PeraZver/Microwave-Transmitter/SW/Firmware/RSSI_Readout/RSSI_Readout.ino

/* 
 *  ADC readout from RSSI detectors LMH2120.
 *  
 *  Example based on example for analogRead from Teensy examples.
*  You can change the number of averages, bits of resolution and also the comparison value or range.
*  
*  Pero, August 2017
*/


#include <ADC.h>

const int readPin = A0; // ADC0
const int readPin2 = A1; // ADC1

ADC *adc = new ADC(); // adc object;

void setup() {

    pinMode(readPin, INPUT); 
    pinMode(readPin2, INPUT); 


    Serial.begin(9600);

    Serial.println("RSSI detectors interface");
    Serial.println("v0.0");
    Serial.println("Pero, August 2017");
    Serial.println("");

    ///// ADC0 ////
    // reference can be ADC_REF_3V3, ADC_REF_1V2 (not for Teensy LC) or ADC_REF_EXT.
    //adc->setReference(ADC_REF_1V2, ADC_0); // change all 3.3 to 1.2 if you change the reference to 1V2

    adc->setAveraging(32); // set number of averages
    adc->setResolution(12); // set bits of resolution

    // it can be ADC_VERY_LOW_SPEED, ADC_LOW_SPEED, ADC_MED_SPEED, ADC_HIGH_SPEED_16BITS, ADC_HIGH_SPEED or ADC_VERY_HIGH_SPEED
    // see the documentation for more information
    adc->setConversionSpeed(ADC_HIGH_SPEED); // change the conversion speed
    // it can be ADC_VERY_LOW_SPEED, ADC_LOW_SPEED, ADC_MED_SPEED, ADC_HIGH_SPEED or ADC_VERY_HIGH_SPEED
    adc->setSamplingSpeed(ADC_HIGH_SPEED); // change the sampling speed

    //adc->enableInterrupts(ADC_0);

    // always call the compare functions after changing the resolution!
    //adc->enableCompare(1.0/3.3*adc->getMaxValue(ADC_0), 0, ADC_0); // measurement will be ready if value < 1.0V
    //adc->enableCompareRange(1.0*adc->getMaxValue(ADC_0)/3.3, 2.0*adc->getMaxValue(ADC_0)/3.3, 0, 1, ADC_0); // ready if value lies out of [1.0,2.0] V

    ////// ADC1 /////
    #if ADC_NUM_ADCS>1
    adc->setAveraging(32, ADC_1); // set number of averages
    adc->setResolution(16, ADC_1); // set bits of resolution
    adc->setConversionSpeed(ADC_VERY_LOW_SPEED, ADC_1); // change the conversion speed
    adc->setSamplingSpeed(ADC_VERY_LOW_SPEED, ADC_1); // change the sampling speed

    // always call the compare functions after changing the resolution!
    //adc->enableCompare(1.0/3.3*adc->getMaxValue(ADC_1), 0, ADC_1); // measurement will be ready if value < 1.0V
    //adc->enableCompareRange(1.0*adc->getMaxValue(ADC_1)/3.3, 2.0*adc->getMaxValue(ADC_1)/3.3, 0, 1, ADC_1); // ready if value lies out of [1.0,2.0] V
    #endif

    Serial.println("End setup");

}

int value;
int value2;

void loop() {

    value = adc->analogRead(readPin); // read a new value, will return ADC_ERROR_VALUE if the comparison is false.

    Serial.print("Pin: ");
    Serial.print(readPin);
    Serial.print(", value ADC0: ");
    Serial.println(value*3.3/adc->getMaxValue(ADC_0), DEC);

    #if ADC_NUM_ADCS>1
    value2 = adc->analogRead(readPin2, ADC_1);

    Serial.print("Pin: ");
    Serial.print(readPin2);
    Serial.print(", value ADC1: ");
    Serial.println(value2*3.3/adc->getMaxValue(ADC_1), DEC);
    #endif

    /* fail_flag contains all possible errors,
        They are defined in  ADC_Module.h as

        ADC_ERROR_OTHER
        ADC_ERROR_CALIB
        ADC_ERROR_WRONG_PIN
        ADC_ERROR_ANALOG_READ
        ADC_ERROR_COMPARISON
        ADC_ERROR_ANALOG_DIFF_READ
        ADC_ERROR_CONT
        ADC_ERROR_CONT_DIFF
        ADC_ERROR_WRONG_ADC
        ADC_ERROR_SYNCH

        You can compare the value of the flag with those masks to know what's the error.
    */

    if(adc->adc0->fail_flag) {
        Serial.print("ADC0 error flags: 0x");
        Serial.println(adc->adc0->fail_flag, HEX);
        if(adc->adc0->fail_flag == ADC_ERROR_COMPARISON) {
            adc->adc0->fail_flag &= ~ADC_ERROR_COMPARISON; // clear that error
            Serial.println("Comparison error in ADC0");
        }
    }
    #if ADC_NUM_ADCS>1
    if(adc->adc1->fail_flag) {
        Serial.print("ADC1 error flags: 0x");
        Serial.println(adc->adc1->fail_flag, HEX);
        if(adc->adc1->fail_flag == ADC_ERROR_COMPARISON) {
            adc->adc1->fail_flag &= ~ADC_ERROR_COMPARISON; // clear that error
            Serial.println("Comparison error in ADC1");
        }
    }
    #endif

    digitalWriteFast(LED_BUILTIN, !digitalReadFast(LED_BUILTIN));

    delay(500);
}

// If you enable interrupts make sure to call readSingle() to clear the interrupt.
void adc0_isr() {
        adc->adc0->readSingle();
}
