PeraZver/Microwave-Transmitter/SW/Firmware/Basic/src/MAX2871.cpp

#include <MAX2871.h>

//Setting temperature read and MUX readout
uint32_t regInitValues[6] = { EN_INT | N_SET | F_SET | REG_0,
                              CPL | CPT | PHASE | M_SET | REG_1,
                              0x00005E42 | LDF,
                              0xE8000013,
                              0x618160DC | DIVA,
                              0x00400005 | F01}; // MUX[3] = 1, ADCM = 001, ADCS = 1

uint32_t MAX2871_Registers[6] = {0}; //Working registers, that will be changed in code
// ADC selection varible
byte adc_mode = 0b001;  // 001 for temperature, 100 for V tune.

SPISettings MAX2871_SPISettings(1000000, MSBFIRST, SPI_MODE0);



void MAX2871_Init (){
  //Upon power-up, the registers should be programmed
  //twice with at least a 20ms pause between writes.
  //Register programming order should be address 0x05,
  //0x04, 0x03, 0x02, 0x01, and 0x00.

  // Enable MAX3871 chip
  pinMode(MAX2871_CE, OUTPUT);
  digitalWrite(MAX2871_CE, HIGH);

  // set the slave select pin as an output:
  pinMode (MAX2871_SS, OUTPUT);
  digitalWrite (MAX2871_SS, HIGH);

  //Disable RF output
  pinMode(MAX2871_RF_EN, OUTPUT);
  digitalWrite (MAX2871_RF_EN, LOW);

  // Writing 2 times
  for (int j = 0; j < 2; j++){
    for (int i = 5; i >= 0; i--){   // 6 write registers
        MAX2871_SPI_tx (regInitValues[i]);
        MAX2871_Registers[i] = regInitValues[i];    // write init values into working registers
    }
    delay(20);
  }

   MAX2871_SPI_Init();
}

void MAX2871_Read(char adc_select){
  /*
   * Reading register 6 over SPI. Register contains data from ADC and VCO selection.
   * ADC can read either temperature or VCO tuning voltage.
   */

   uint32_t spi_data = 0;
   uint8_t spi_packet[4] = {0};
   uint8_t ADC_data = 0;
   float data = 0;
   signed char i;

   Serial.println("Setting MAX2871 ADC ...");

   switch (adc_select){   // Choose whether to read temperature or VCO voltage
     case 'v':
         adc_mode = 0b100;
         break;

     case 't':
         adc_mode = 0b001;
         break;

    default:   // default value is read temperature
        adc_mode = 0b001;
   }

   MAX2871_ADC_Init();

   Serial.println("Reading data from MAX2871 ...");
   MAX2871_SPI_tx(spi_data | 6);   // "... last 3 bits must be 110 to indicate register 6."

   SPI.beginTransaction(MAX2871_SPISettings);  // start new clock sequence. No need to change SS to low.
   for ( i = 0; i < 4; i++)   {
       spi_packet[i] = SPI.transfer(0x00);   // read from SPI shift register 4 times
   }
   SPI.endTransaction();

   Serial.println("Data read:");
   for ( i = 0; i < 4; i++){
     //Serial.println(spi_packet[i], HEX);
     spi_data |= spi_packet[i];
     if ( i != 3)
         spi_data = spi_data << 8;
   }
   spi_data = spi_data << 2; //one clk period delay
   Serial.println(spi_data, HEX);
   Serial.println("Reading done!");

   if (spi_data & ADCV)
     Serial.println("ADC data valid!");
   else
     Serial.println("ADC data invalid!");
   ADC_data = ( spi_data & ADC_mask ) >> 16;
   Serial.print("ADC data: ");
   Serial.print(ADC_data);

  if (adc_mode == 1){
      data = 95 - 1.14*ADC_data;
      Serial.print("\nTemperature: ");
  }
  else{
      data = 0.315 + 0.0165*ADC_data;
      Serial.print("\nVCO voltage: ");
  }
  Serial.print(data);


  if (spi_data & VASA)
    Serial.println("\nVCO Autoselect searching");
  else
    Serial.println("\nVAS Completed");

  Serial.print("Current VCO: ");
  Serial.println((spi_data & V) >> 3);
  //Serial.println("Reseting ADC");
  MAX2871_ADC_Reset();
}

void MAX2871_SPI_tx(uint32_t spi_data){
  /*
   * This function takes 32-bit data and parses it on four 8-bit packets that Teensy transmitts. The 29 most-significant
   * bits (MSBs) are data, and the three least-significant bits (LSBs) are the register address.
   */

    signed char i = 0;
    uint8_t spi_package[4] = {0};
    // store 32-bit integer into 4 bytes
    for ( i = 0; i < 4; i++) {
       spi_package[i] = (spi_data & (0xFF << 8*i)) >> ( 8*i ) ;
       //Serial.println(spi_package[i], HEX);
    }

    //Serial.println("Sending data to MAX2871: ");
    //Serial.println(spi_data, HEX);
    digitalWrite(MAX2871_SS,LOW);
    SPI.beginTransaction(MAX2871_SPISettings);

    for ( i = 3; i >= 0; i--)
         SPI.transfer(spi_package[i]);

    digitalWrite(MAX2871_SS,HIGH);
    SPI.endTransaction();
    //Serial.println("SPI done!");
    delay(20);
}

void MAX2871_ADC_Init(void){
  /*
   * Initialize ADC in MAX2871 for temperature or tune voltage readout. Must be
   * sequentially written, otherwise it won't work.
   */
   byte ADCM;
   ADCM = adc_mode << 3;

   MAX2871_Registers[3] |= CDIV;
   MAX2871_SPI_tx(MAX2871_Registers[3]);
   MAX2871_Registers[5] |= ADCM;
   MAX2871_SPI_tx(MAX2871_Registers[5]);
   MAX2871_Registers[5] |= ADCS;
   MAX2871_SPI_tx(MAX2871_Registers[5]);
   delay(0.1);
}

void MAX2871_ADC_Reset(void){
 /*
 * Apparently ADC won't work if ADCS is constantly on. For that reason, I'll need to reset it after every read.
 */
 MAX2871_Registers[5] &= ~(0b111 << 3);
 MAX2871_Registers[5] &= ~(ADCS);
 MAX2871_SPI_tx(MAX2871_Registers[5]);

}

void MAX2871_SPI_Init(){
  /* Set MUX bits to enable reg6 readout over SPI.
   *
   */
   MAX2871_Registers[5] |= MUX_5;
   MAX2871_SPI_tx(MAX2871_Registers[5]);
   MAX2871_Registers[2] |= MUX_2;
   MAX2871_SPI_tx(MAX2871_Registers[2]);

}

void MAX2871_RFA_Enable(){
  /* Activates RF A output. */
  MAX2871_Registers[4] |= RFA_EN;
  MAX2871_SPI_tx(MAX2871_Registers[4]);
  digitalWrite(MAX2871_RF_EN, HIGH);

}

void MAX2871_RFB_Enable(){
  /* Activates RF B output. */
  MAX2871_Registers[4] |= RFB_EN;
  MAX2871_SPI_tx(MAX2871_Registers[4]);
  digitalWrite(MAX2871_RF_EN, HIGH);

}

void MAX2871_RFA_Disable(){
  /* Activates RF A output. */
  MAX2871_Registers[4] &= ~RFA_EN;
  MAX2871_SPI_tx(MAX2871_Registers[4]);
  digitalWrite(MAX2871_RF_EN, LOW);

}

void MAX2871_RFB_Disable(){
  /* Activates RF B output. */
  MAX2871_Registers[4] &= ~RFB_EN;
  MAX2871_SPI_tx(MAX2871_Registers[4]);
  digitalWrite(MAX2871_RF_EN, LOW);

}

void MAX2871_Print_Registers(void){
  /* Printout current register settings */
  for (int i = 0; i<6; i++)
    Serial.println(MAX2871_Registers[i], HEX);
}

void MAX2871_RFA_Power(char power){
  /* Sets the power to the RF A output */
  MAX2871_RFA_Disable();
  MAX2871_Registers[4] &= ~(3 << 3); // "clean" power bits (actually set to min)
  MAX2871_Registers[4] |= (power << 3); // Set desired value
  MAX2871_RFA_Enable();
}

void MAX2871_RFA_SelectPower(char power){

  switch (power) {
    case '1':
        Serial.println("Setting power to -4 dBm");
        MAX2871_RFA_Power(0);
        break;

    case '2':
        Serial.println("Setting power to -1 dBm");
        MAX2871_RFA_Power(1);
        break;

    case '3':
        Serial.println("Setting power to 2 dBm");
        MAX2871_RFA_Power(2);
        break;

    case '4':
        Serial.println("Setting power to 5 dBm");
        MAX2871_RFA_Power(3);
        break;

    default:
        ;
  }

}

void MAX2871_SetN(uint16_t N){
    /* sets 16 integer divison value N bits in register 0[30:15]*/

    if ((N < 16) || (N > 65535))
        Serial.println("Selected value invalid!");
    else{
        Serial.print("selected N is: ");
        Serial.print(N);
        Serial.println("");
        MAX2871_Registers[0] &= (~N_MASK);
        MAX2871_Registers[0] |= (N << 15);
        MAX2871_SPI_tx(MAX2871_Registers[0]);
    }
}

void MAX2871_SetF(uint16_t F){
    /* sets 12 fractional divison value F bits in register 0[14:3]*/

    if (F > 4095)
        Serial.println("Selected value invalid!");
    else{
        // Serial.print("selected F is: ");
        // Serial.print(F);
        // Serial.println("");
        MAX2871_Registers[0] &= (~F_MASK);
        MAX2871_Registers[0] |= (F << 3 );
        MAX2871_SPI_tx(MAX2871_Registers[0]);
    }
}

void MAX2871_SetDIVA(char diva){
    /* sets 3 bit integer divison at the RF output DIVA (reg4[22:20])*/

        Serial.print("Divide factor set to: ");
        Serial.print(1 << (diva-48));
        Serial.println("");
        MAX2871_Registers[4] &= (~DIVA_MASK);
        MAX2871_Registers[4] |= ((diva - 48) << 20);
        MAX2871_SPI_tx(MAX2871_Registers[4]);
}

void MAX2871_SetR(uint16_t R){
    /* sets 16 integer divison value N bits in register 0[30:15]*/

    if (R > 1023)
        Serial.println("Selected value invalid!");
    else{
        Serial.print("selected R is: ");
        Serial.print(R);
        Serial.println("");
        MAX2871_Registers[2] &= (~R_MASK);
        MAX2871_Registers[2] |= (R << 14);
        MAX2871_SPI_tx(MAX2871_Registers[2]);
        MAX2871_SPI_tx(MAX2871_Registers[0]);  // bits R are double buffered
    }
}

void MAX2871_SetM(uint16_t M){
    /* sets 16 integer divison value N bits in register 0[30:15]*/

    if ((M < 2) || (M > 4095))
        Serial.println("Selected value invalid!");
    else{
        Serial.print("selected M is: ");
        Serial.print(M);
        Serial.println("");
        MAX2871_Registers[1] &= (~M_MASK);
        MAX2871_Registers[1] |= (M << 3);
        MAX2871_SPI_tx(MAX2871_Registers[1]);
        MAX2871_SPI_tx(MAX2871_Registers[0]);  // bits M are double buffered
    }
}

void MAX2871_SetFracMode(){
   /* Sets MAX2871 to fractional mode */
   MAX2871_Registers[0] &= ~EN_INT;
   MAX2871_Registers[2] &= ~LDF;
   MAX2871_SPI_tx(MAX2871_Registers[2]);
   MAX2871_SPI_tx(MAX2871_Registers[0]);
}

void MAX2871_SetIntMode(){
  /* Sets MAX2871 to integer mode */
  MAX2871_Registers[0] |= EN_INT;
  MAX2871_Registers[2] |= LDF;
  MAX2871_SPI_tx(MAX2871_Registers[2]);
  MAX2871_SPI_tx(MAX2871_Registers[0]);
}

void MAX2871_Sweep(char divider_type, uint16_t a, uint16_t b, uint16_t dt){
  /* Sweeps value of N or F between a and b */
  uint16_t i = 0;

  if (divider_type == 'N') {
    for (i = a; i < b; i ++){
      MAX2871_SetN(i);
      delay(dt);
    }
  }
  else if (divider_type == 'F') {
    for (i = a; i < b; i ++){
      MAX2871_SetF(i);
      delay(dt);
    }
  }
  else ;

}
